ctebow/xm125/benchmarking/data/distance_back_pvc_7-20-10_v2.csv

trial | register | rdistance | strength | edistance
0 | 0.0 | 216.0 | -12465.0 | 200
0 | 0.0 | 213.0 | -12368.0 | 200
0 | 0.0 | 214.0 | -12081.0 | 200
0 | 0.0 | 214.0 | -12199.0 | 200
0 | 0.0 | 214.0 | -11961.0 | 200
0 | 0.0 | 213.0 | -12363.0 | 200
0 | 0.0 | 214.0 | -12004.0 | 200
0 | 0.0 | 214.0 | -12587.0 | 200
0 | 0.0 | 214.0 | -12501.0 | 200
0 | 0.0 | 214.0 | -12306.0 | 200
0 | 0.0 | 214.0 | -12493.0 | 200
0 | 0.0 | 214.0 | -11685.0 | 200
0 | 0.0 | 214.0 | -12036.0 | 200
0 | 0.0 | 214.0 | -12343.0 | 200
0 | 0.0 | 213.0 | -12458.0 | 200
0 | 0.0 | 214.0 | -12018.0 | 200
0 | 0.0 | 213.0 | -12358.0 | 200
0 | 0.0 | 215.0 | -11960.0 | 200
0 | 0.0 | 215.0 | -11908.0 | 200
0 | 0.0 | 214.0 | -12010.0 | 200
0 | 0.0 | 214.0 | -12074.0 | 200
0 | 0.0 | 214.0 | -12187.0 | 200
0 | 0.0 | 215.0 | -12173.0 | 200
0 | 0.0 | 214.0 | -12096.0 | 200
0 | 0.0 | 214.0 | -12361.0 | 200
0 | 0.0 | 216.0 | -12095.0 | 200
0 | 0.0 | 215.0 | -12318.0 | 200
0 | 0.0 | 215.0 | -12212.0 | 200
0 | 0.0 | 215.0 | -12123.0 | 200
0 | 0.0 | 214.0 | -12176.0 | 200
0 | 0.0 | 212.0 | -12204.0 | 200
0 | 0.0 | 215.0 | -12554.0 | 200
0 | 0.0 | 214.0 | -12203.0 | 200
0 | 0.0 | 213.0 | -12629.0 | 200
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
