ctebow/xm125/benchmarking/data/distance_dual_pvc_5-7-2.csv

trial | register | rdistance | strength | edistance
0 | 0.0 | 227.0 | -92.0 | 70
0 | 1.0 | 73.0 | -8168.0 | 70
0 | 2.0 | 139.0 | -12555.0 | 70
0 | 10.0 | 145.0 | -11551.0 | 70
0 | 11.0 | 214.0 | -14989.0 | 70
0 | 12.0 | 79.0 | -21491.0 | 70
0 | 0.0 | 227.0 | -463.0 | 70
0 | 1.0 | 72.0 | -8329.0 | 70
0 | 2.0 | 139.0 | -12848.0 | 70
0 | 10.0 | 145.0 | -11428.0 | 70
0 | 11.0 | 213.0 | -15304.0 | 70
0 | 12.0 | 79.0 | -21496.0 | 70
0 | 0.0 | 227.0 | -316.0 | 70
0 | 1.0 | 73.0 | -8385.0 | 70
0 | 2.0 | 138.0 | -12825.0 | 70
0 | 10.0 | 145.0 | -11389.0 | 70
0 | 11.0 | 214.0 | -15200.0 | 70
0 | 12.0 | 79.0 | -21544.0 | 70
0 | 0.0 | 227.0 | -402.0 | 70
0 | 1.0 | 73.0 | -8335.0 | 70
0 | 2.0 | 138.0 | -12951.0 | 70
0 | 10.0 | 145.0 | -11580.0 | 70
0 | 11.0 | 212.0 | -15711.0 | 70
0 | 12.0 | 79.0 | -21874.0 | 70
0 | 0.0 | 228.0 | -327.0 | 70
0 | 1.0 | 73.0 | -8282.0 | 70
0 | 2.0 | 138.0 | -12845.0 | 70
0 | 10.0 | 145.0 | -11375.0 | 70
0 | 11.0 | 212.0 | -15507.0 | 70
0 | 12.0 | 79.0 | -21799.0 | 70
0 | 0.0 | 227.0 | -163.0 | 70
0 | 1.0 | 72.0 | -8402.0 | 70
0 | 2.0 | 138.0 | -12600.0 | 70
0 | 10.0 | 146.0 | -11326.0 | 70
0 | 11.0 | 212.0 | -15585.0 | 70
0 | 12.0 | 79.0 | -21554.0 | 70
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
