ctebow/xm125/benchmarking/data/dual_test_pvc.csv

trial | register | rdistance | strength | edistance
0 | 0.0 | 217.0 | -3923.0 | 200
0 | 1.0 | 56.0 | -10188.0 | 200
0 | 2.0 | 140.0 | -14353.0 | 200
0 | 10.0 | 75.0 | -6194.0 | 200
0 | 11.0 | 150.0 | -14244.0 | 200
0 | 12.0 | 234.0 | -18883.0 | 200
0 | 0.0 | 216.0 | -3801.0 | 200
0 | 1.0 | 56.0 | -10167.0 | 200
0 | 2.0 | 139.0 | -14413.0 | 200
0 | 10.0 | 75.0 | -6217.0 | 200
0 | 11.0 | 149.0 | -14395.0 | 200
0 | 12.0 | 225.0 | -17018.0 | 200
0 | 0.0 | 216.0 | -4111.0 | 200
0 | 1.0 | 56.0 | -10416.0 | 200
0 | 2.0 | 139.0 | -14208.0 | 200
0 | 10.0 | 75.0 | -6186.0 | 200
0 | 11.0 | 150.0 | -14420.0 | 200
0 | 12.0 | 228.0 | -16570.0 | 200
0 | 0.0 | 217.0 | -4124.0 | 200
0 | 1.0 | 57.0 | -10090.0 | 200
1 | 0.0 | 216.0 | -4050.0 | 190
1 | 1.0 | 56.0 | -10276.0 | 190
1 | 2.0 | 139.0 | -14253.0 | 190
1 | 10.0 | 75.0 | -6238.0 | 190
1 | 11.0 | 149.0 | -14226.0 | 190
1 | 12.0 | 226.0 | -15671.0 | 190
1 | 0.0 | 216.0 | -4202.0 | 190
1 | 1.0 | 56.0 | -10312.0 | 190
1 | 2.0 | 140.0 | -14516.0 | 190
1 | 10.0 | 75.0 | -6210.0 | 190
1 | 11.0 | 149.0 | -14783.0 | 190
1 | 12.0 | 223.0 | -16866.0 | 190
1 | 0.0 | 216.0 | -3955.0 | 190
1 | 1.0 | 56.0 | -10224.0 | 190
1 | 2.0 | 140.0 | -14550.0 | 190
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
